AdityaWadhwa/Chidiya-Udd/TalkingChidiyaUddCodeFinal/PCD8544.h

#ifndef PCD8544_H_
#define PCD8544_H_

#define PCD8544_POWERDOWN 0x04
#define PCD8544_ENTRYMODE 0x02
#define PCD8544_EXTENDEDINSTRUCTION 0x01

#define PCD8544_DISPLAYBLANK 0x0
#define PCD8544_DISPLAYNORMAL 0x4
#define PCD8544_DISPLAYALLON 0x1
#define PCD8544_DISPLAYINVERTED 0x5

// H = 0
#define PCD8544_FUNCTIONSET 0x20
#define PCD8544_DISPLAYCONTROL 0x08
#define PCD8544_SETYADDR 0x40
#define PCD8544_SETXADDR 0x80
#define PCD8544_HPIXELS 84
#define PCD8544_VBANKS 6
#define PCD8544_MAXBYTES 504 // PCD8544_HPIXELS * PCD8544_VBANKS

// H = 1
#define PCD8544_SETTEMP 0x04
#define PCD8544_SETBIAS 0x10
#define PCD8544_SETVOP 0x80

//transform
#define NONE 0x00
#define FLIP_H 0x01
#define FLIP_V 0x02
#define ROTATE 0x04 // 90 deg CW
#define ROTATE_90_CW ROTATE
#define ROTATE_90_CCW (FLIP_H | FLIP_V | ROTATE)
#define ROTATE_180 (FLIP_H | FLIP_V)

static const char font[][5] = { // basic font
{0x00, 0x00, 0x00, 0x00, 0x00} // 20
,{0x00, 0x00, 0x5f, 0x00, 0x00} // 21 !
,{0x00, 0x07, 0x00, 0x07, 0x00} // 22 "
,{0x14, 0x7f, 0x14, 0x7f, 0x14} // 23 #
,{0x24, 0x2a, 0x7f, 0x2a, 0x12} // 24 $
,{0x23, 0x13, 0x08, 0x64, 0x62} // 25 %
,{0x36, 0x49, 0x55, 0x22, 0x50} // 26 &
,{0x00, 0x05, 0x03, 0x00, 0x00} // 27 '
,{0x00, 0x1c, 0x22, 0x41, 0x00} // 28 (
,{0x00, 0x41, 0x22, 0x1c, 0x00} // 29 )
,{0x14, 0x08, 0x3e, 0x08, 0x14} // 2a *
,{0x08, 0x08, 0x3e, 0x08, 0x08} // 2b +
,{0x00, 0x50, 0x30, 0x00, 0x00} // 2c ,
,{0x08, 0x08, 0x08, 0x08, 0x08} // 2d -
,{0x00, 0x60, 0x60, 0x00, 0x00} // 2e .
,{0x20, 0x10, 0x08, 0x04, 0x02} // 2f /
,{0x3e, 0x51, 0x49, 0x45, 0x3e} // 30 0
,{0x00, 0x42, 0x7f, 0x40, 0x00} // 31 1
,{0x42, 0x61, 0x51, 0x49, 0x46} // 32 2
,{0x21, 0x41, 0x45, 0x4b, 0x31} // 33 3
,{0x18, 0x14, 0x12, 0x7f, 0x10} // 34 4
,{0x27, 0x45, 0x45, 0x45, 0x39} // 35 5
,{0x3c, 0x4a, 0x49, 0x49, 0x30} // 36 6
,{0x01, 0x71, 0x09, 0x05, 0x03} // 37 7
,{0x36, 0x49, 0x49, 0x49, 0x36} // 38 8
,{0x06, 0x49, 0x49, 0x29, 0x1e} // 39 9
,{0x00, 0x36, 0x36, 0x00, 0x00} // 3a :
,{0x00, 0x56, 0x36, 0x00, 0x00} // 3b ;
,{0x08, 0x14, 0x22, 0x41, 0x00} // 3c <
,{0x14, 0x14, 0x14, 0x14, 0x14} // 3d =
,{0x00, 0x41, 0x22, 0x14, 0x08} // 3e >
,{0x02, 0x01, 0x51, 0x09, 0x06} // 3f ?
,{0x32, 0x49, 0x79, 0x41, 0x3e} // 40 @
,{0x7e, 0x11, 0x11, 0x11, 0x7e} // 41 A
,{0x7f, 0x49, 0x49, 0x49, 0x36} // 42 B
,{0x3e, 0x41, 0x41, 0x41, 0x22} // 43 C
,{0x7f, 0x41, 0x41, 0x22, 0x1c} // 44 D
,{0x7f, 0x49, 0x49, 0x49, 0x41} // 45 E
,{0x7f, 0x09, 0x09, 0x09, 0x01} // 46 F
,{0x3e, 0x41, 0x49, 0x49, 0x7a} // 47 G
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
,{0x00, 0x06, 0x09, 0x09, 0x06} // 7f Deg Symbol
};

#endif /*PCD8544_H_*/
