AdityaWadhwa/Chidiya-Udd/sendData.py

from time import sleep
from tqdm import tqdm
import sys
import serial
import struct
ser = serial.Serial('COM4', 57600) 

i = 0

data = [
[

128, 128, 128, 128, 128, 127, 128, 128, # 0-7
128, 128, 128, 127, 128, 127, 128, 127, # 8-15
128, 127, 128, 127, 128, 127, 128, 127, # 16-23
128, 127, 128, 128, 128, 127, 128, 127, # 24-31
128, 127, 128, 127, 128, 127, 128, 127, # 32-39
128, 128, 127, 128, 128, 127, 128, 127, # 40-47
128, 128, 127, 128, 127, 128, 127, 128, # 48-55
127, 128, 127, 128, 127, 128, 127, 128, # 56-63
128, 128, 127, 128, 127, 128, 127, 128, # 64-71
128, 127, 128, 127, 128, 127, 128, 128, # 72-79
127, 128, 128, 128, 128, 128, 127, 128, # 80-87
128, 127, 128, 127, 128, 128, 128, 128, # 88-95
127, 128, 127, 128, 127, 128, 127, 128, # 96-103
128, 127, 128, 127, 128, 127, 128, 128, # 104-111
127, 128, 128, 128, 128, 127, 128, 127, # 112-119
128, 127, 127, 128, 127, 127, 128, 128, # 120-127
127, 128, 128, 127, 128, 127, 128, 127, # 128-135
128, 127, 127, 128, 128, 127, 128, 128, # 136-143
127, 128, 128, 127, 127, 128, 127, 128, # 144-151
128, 128, 128, 128, 128, 128, 127, 128, # 152-159
127, 127, 128, 127, 127, 128, 128, 128, # 160-167
127, 128, 127, 128, 127, 128, 128, 127, # 168-175
128, 128, 127, 128, 128, 128, 127, 127, # 176-183
128, 128, 128, 128, 128, 128, 128, 128, # 184-191
127, 128, 127, 127, 127, 128, 127, 128, # 192-199
128, 128, 128, 128, 128, 127, 127, 128, # 200-207
127, 127, 128, 128, 127, 128, 128, 127, # 208-215
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
]
] 


sleep(5)
#ser.write(data.encode("utf-8"))
#ser.close()

i=0
j=0

for d in data:

	j+=1
	print("Writting "+ str(j) + " of " + str(len(data)))


	for i in tqdm(range(len(d))):

		x = d[i]
    
		value = str(x) + "\n"

		ser.write(value.encode("utf-8"))

		#sleep(.001)


ser.close()
